openhardwaresv/curso_smd/dsn/auxiliar/Renders SMD/Board_top.png

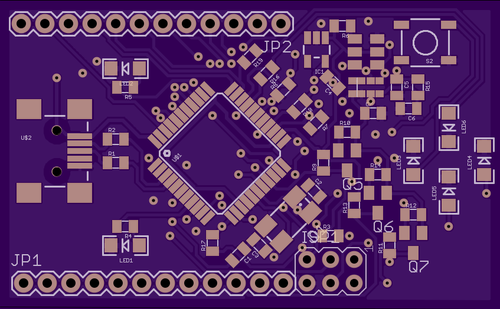
dsn/auxiliar/Renders SMD/Board_top.png
