openhardwaresv/curso_smd/dsn/auxiliar/Renders SMD/drills.png

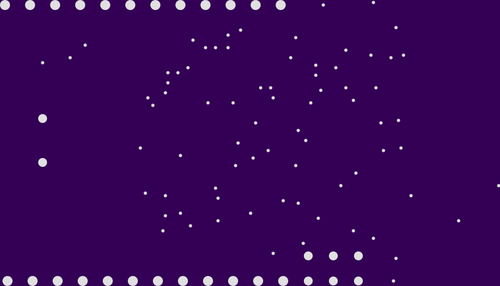
dsn/auxiliar/Renders SMD/drills.png
