openhardwaresv/curso_smd/dsn/auxiliar/Renders SMD/bottom_soldermask.png

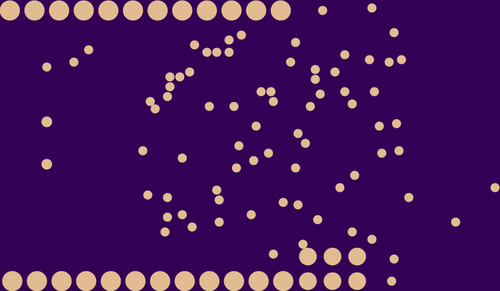
dsn/auxiliar/Renders SMD/bottom_soldermask.png
