openhardwaresv/curso_smd/dsn/auxiliar/Renders SMD/TOP_soldermask.png

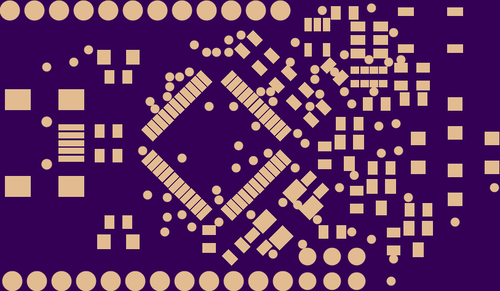
dsn/auxiliar/Renders SMD/TOP_soldermask.png
